ninezerozeronine/chip-computer/docs/software/source/eight_bit_computer.rst

eight\_bit\_computer package
============================

Subpackages
-----------

.. toctree::

    eight_bit_computer.operations

Submodules
----------

.. toctree::

   eight_bit_computer.assembler
   eight_bit_computer.assembly_summary
   eight_bit_computer.assembly_validity
   eight_bit_computer.bitdef
   eight_bit_computer.cli
   eight_bit_computer.data_structures
   eight_bit_computer.exceptions
   eight_bit_computer.export
   eight_bit_computer.language_defs
   eight_bit_computer.main
   eight_bit_computer.number_utils
   eight_bit_computer.operation_utils
   eight_bit_computer.rom
   eight_bit_computer.token_utils

Module contents
---------------

.. automodule:: eight_bit_computer
    :members:
    :undoc-members:
    :show-inheritance:
