ninezerozeronine/chip-computer/logisim/computer_image.png

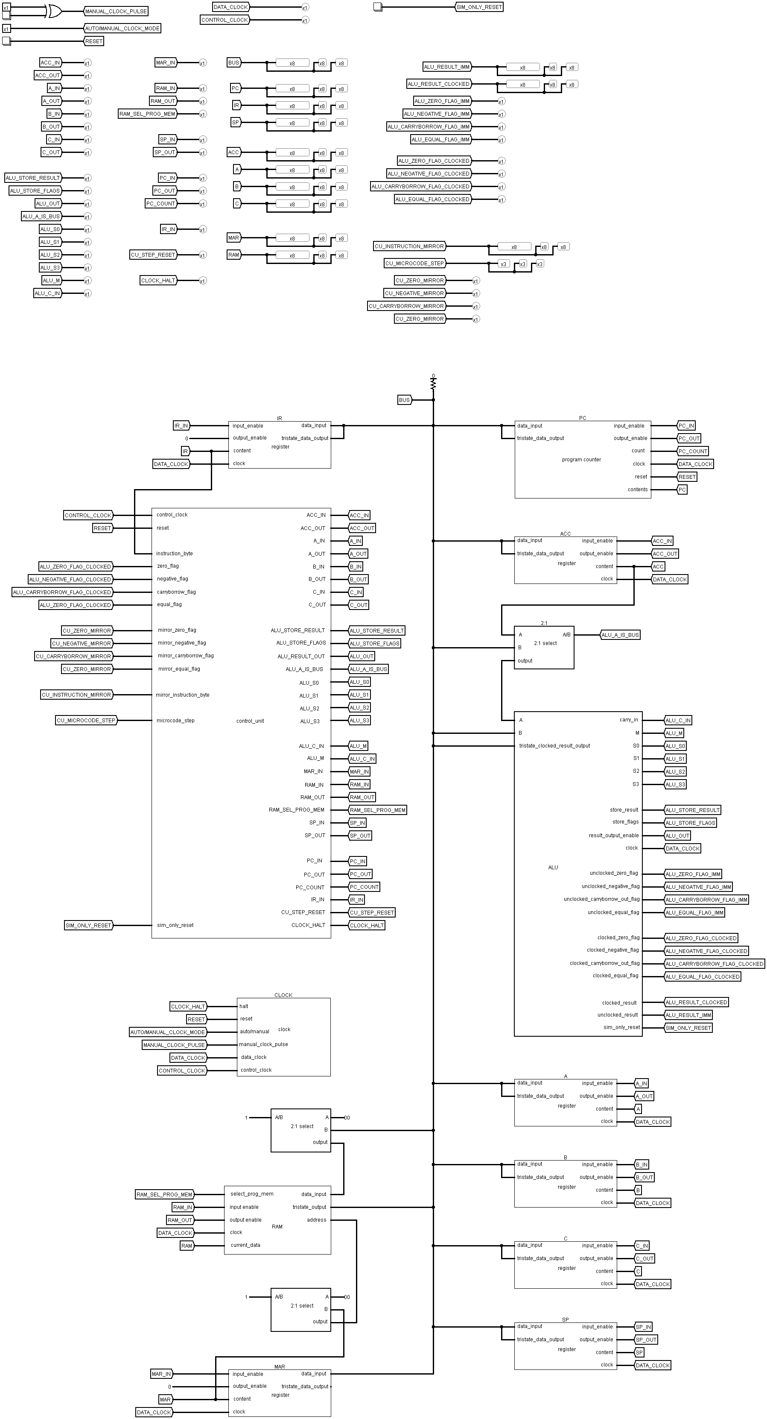
logisim/computer_image.png
